Henkru/novum/novum/art/bottom.png

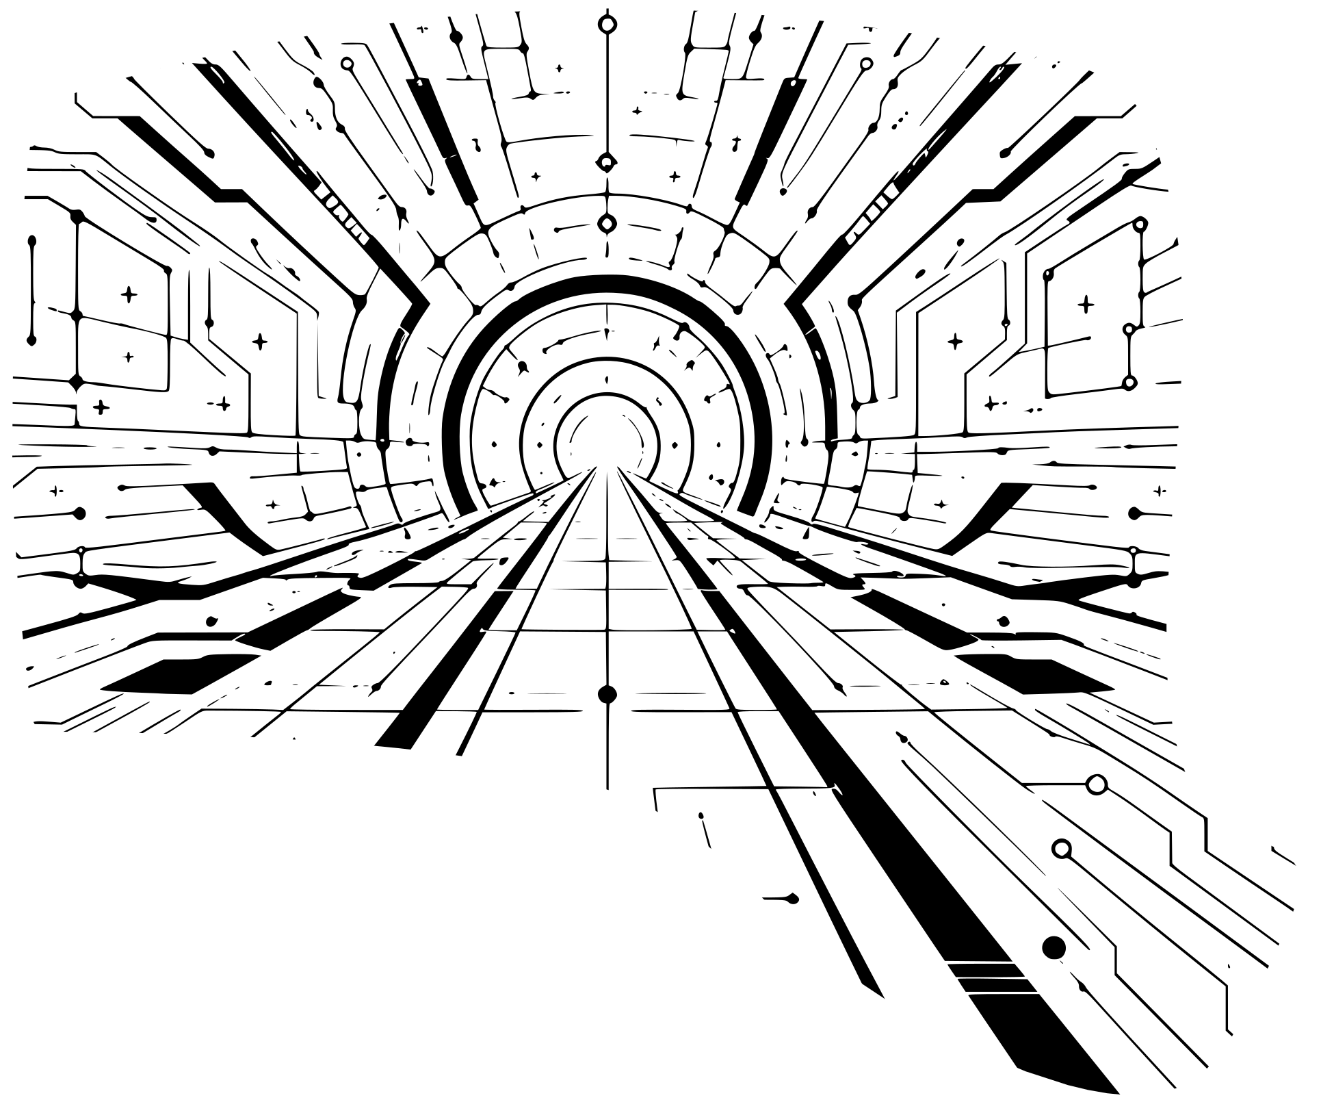
novum/art/bottom.png
